viragored/organ-pipe-foot/foot 1.jpg

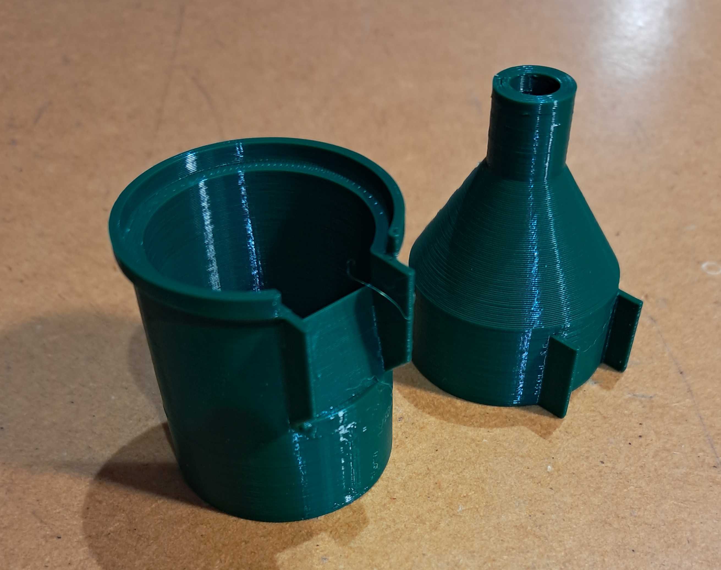
foot 1.jpg
