viragored/organ-pipe-foot/pipe 1.jpg

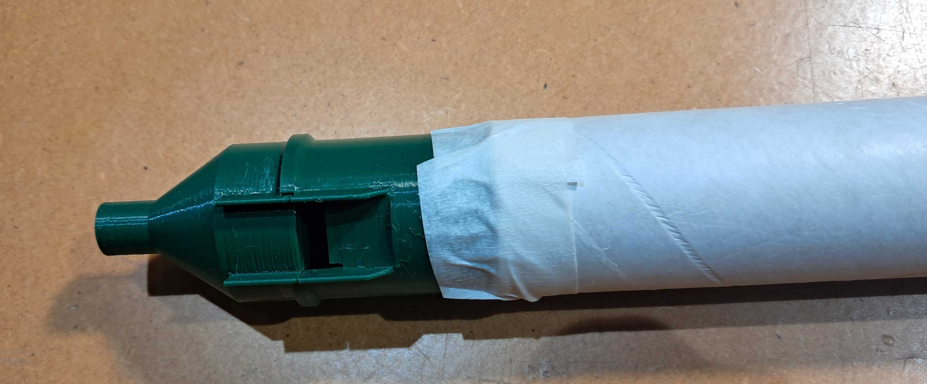
pipe 1.jpg
