viragored/organ-pipe-foot/v2 Pic 3.jpg

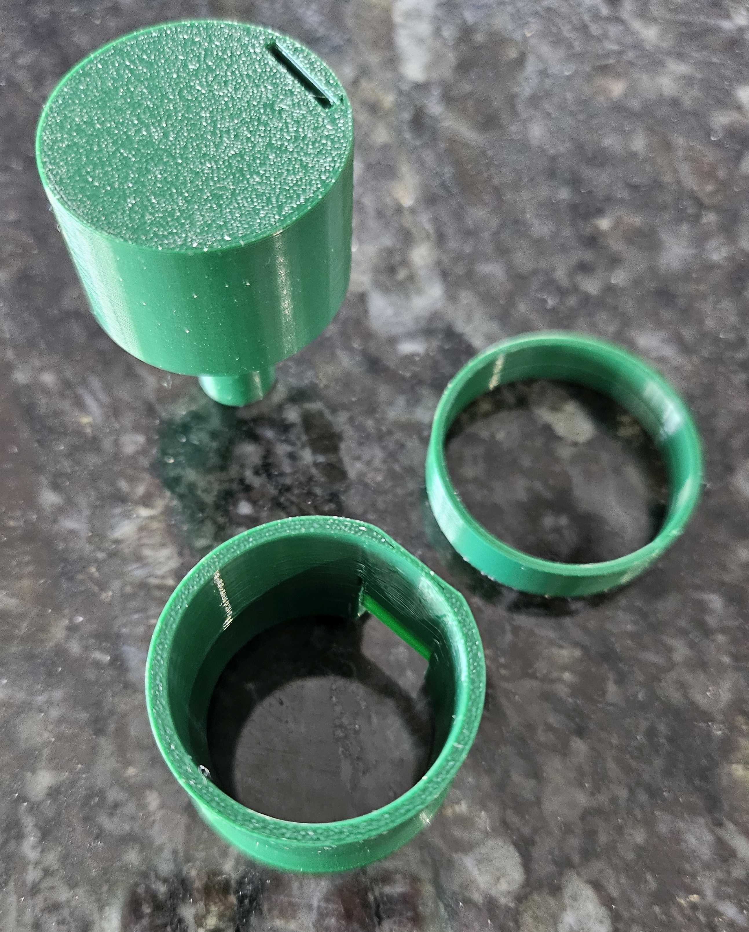
v2 Pic 3.jpg
